JonathanFerron/MiyoCalc40/MiyoCalc40_firmware/cards.cpp

/*
  cards.c

*/

// includes
#include <stdint.h>
#include "cards.h"
#include "fonts.h"
#include "matrix.h"
#include "calc.h"
#include "config.h"

// defines


// structures

// global variables
const action ACT_0 = {KC_0, &enter_number, {0, MCFNULCHAR, MCFNULCHAR, MCFNULCHAR, MCFNULCHAR}};
const action ACT_1 = {KC_1, &enter_number, {1, MCFNULCHAR, MCFNULCHAR, MCFNULCHAR, MCFNULCHAR}};
const action ACT_2 = {KC_2, &enter_number, {2, MCFNULCHAR, MCFNULCHAR, MCFNULCHAR, MCFNULCHAR}};
const action ACT_3 = {KC_3, &enter_number, {3, MCFNULCHAR, MCFNULCHAR, MCFNULCHAR, MCFNULCHAR}};
const action ACT_4 = {KC_4, &enter_number, {4, MCFNULCHAR, MCFNULCHAR, MCFNULCHAR, MCFNULCHAR}};
const action ACT_5 = {KC_5, &enter_number, {5, MCFNULCHAR, MCFNULCHAR, MCFNULCHAR, MCFNULCHAR}};
const action ACT_6 = {KC_6, &enter_number, {6, MCFNULCHAR, MCFNULCHAR, MCFNULCHAR, MCFNULCHAR}};
const action ACT_7 = {KC_7, &enter_number, {7, MCFNULCHAR, MCFNULCHAR, MCFNULCHAR, MCFNULCHAR}};
const action ACT_8 = {KC_8, &enter_number, {8, MCFNULCHAR, MCFNULCHAR, MCFNULCHAR, MCFNULCHAR}};
const action ACT_9 = {KC_9, &enter_number, {9, MCFNULCHAR, MCFNULCHAR, MCFNULCHAR, MCFNULCHAR}};
const action ACT_A = {KC_A, &enter_number, {'A' - MCFLETOFFSET, MCFNULCHAR, MCFNULCHAR, MCFNULCHAR, MCFNULCHAR}};
const action ACT_B = {KC_B, &enter_number, {'B' - MCFLETOFFSET, MCFNULCHAR, MCFNULCHAR, MCFNULCHAR, MCFNULCHAR}};
const action ACT_C = {KC_C, &enter_number, {'C' - MCFLETOFFSET, MCFNULCHAR, MCFNULCHAR, MCFNULCHAR, MCFNULCHAR}};
const action ACT_D = {KC_D, &enter_number, {'D' - MCFLETOFFSET, MCFNULCHAR, MCFNULCHAR, MCFNULCHAR, MCFNULCHAR}};
const action ACT_E = {KC_E, &enter_number, {'E' - MCFLETOFFSET, MCFNULCHAR, MCFNULCHAR, MCFNULCHAR, MCFNULCHAR}};
const action ACT_F = {KC_F, &enter_number, {'F' - MCFLETOFFSET, MCFNULCHAR, MCFNULCHAR, MCFNULCHAR, MCFNULCHAR}};

const action ACT_POINT = {KC_POINT, &enter_decpoint, {MCFNULCHAR, MCFNULCHAR, MCFNULCHAR, MCFNULCHAR, MCFNULCHAR}};  // need to implement a decimal point character in the main font table
const action ACT_CHGSGN = {KC_CHGSGN, &enter_sign, {39, 36, MCFNULCHAR, MCFNULCHAR, MCFNULCHAR}};
const action ACT_EEX = {KC_EEX, &enter_exp, {'E' - MCFLETOFFSET, MCFNULCHAR, MCFNULCHAR, MCFNULCHAR, MCFNULCHAR}};
const action ACT_PI = {KC_PI, &apply_const, {47, MCFNULCHAR, MCFNULCHAR, MCFNULCHAR, MCFNULCHAR}};

const action ACT_ADD = {KC_ADD, &apply_func_2to1, {39, MCFNULCHAR, MCFNULCHAR, MCFNULCHAR, MCFNULCHAR}};
const action ACT_SUBS = {KC_SUBS, &apply_func_2to1, {36, MCFNULCHAR, MCFNULCHAR, MCFNULCHAR, MCFNULCHAR}};
const action ACT_MULT = {KC_MULT, &apply_func_2to1, {'X' - MCFLETOFFSET, MCFNULCHAR, MCFNULCHAR, MCFNULCHAR, MCFNULCHAR}};  // need to implement a multiplication character in the main font table
const action ACT_DIV = {KC_DIV, &apply_func_2to1, {45, MCFNULCHAR, MCFNULCHAR, MCFNULCHAR, MCFNULCHAR}};
const action ACT_POW = {KC_POW, &apply_func_2to1, {'P' - MCFLETOFFSET, 'O' - MCFLETOFFSET, 'W' - MCFLETOFFSET, MCFNULCHAR, MCFNULCHAR}};
const action ACT_ROOT = {KC_ROOT, &apply_func_2to1, {'R' - MCFLETOFFSET, 'O' - MCFLETOFFSET, 'O' - MCFLETOFFSET, 'T' - MCFLETOFFSET, MCFNULCHAR}};
const action ACT_MULTINV = {KC_MULTINV, &apply_func_1to1, {1, 45, 'X' - MCFLETOFFSET, MCFNULCHAR, MCFNULCHAR}};
const action ACT_ABS = {KC_ABS, &apply_func_1to1, {'A' - MCFLETOFFSET, 'B' - MCFLETOFFSET, 'S' - MCFLETOFFSET, MCFNULCHAR, MCFNULCHAR}};
const action ACT_SQRT = {KC_SQRT, &apply_func_1to1, {'S' - MCFLETOFFSET, 'Q' - MCFLETOFFSET, 'R' - MCFLETOFFSET, 'T' - MCFLETOFFSET, MCFNULCHAR}};
const action ACT_SQUARE = {KC_SQUARE, &apply_func_1to1, {'X' - MCFLETOFFSET, 42, 2, MCFNULCHAR, MCFNULCHAR}};
const action ACT_LN = {KC_LN, &apply_func_1to1, {'L' - MCFLETOFFSET, 'N' - MCFLETOFFSET, MCFNULCHAR, MCFNULCHAR, MCFNULCHAR}};
const action ACT_EXP = {KC_EXP, &apply_func_1to1, {'E' - MCFLETOFFSET, 'X' - MCFLETOFFSET, 'P' - MCFLETOFFSET, MCFNULCHAR, MCFNULCHAR}};
const action ACT_FACT = {KC_FACT, &apply_func_1to1, {'F' - MCFLETOFFSET, 'A' - MCFLETOFFSET, 'C' - MCFLETOFFSET, 'T' - MCFLETOFFSET, MCFNULCHAR}};
const action ACT_ROUND = {KC_ROUND, &apply_func_1to1, {'R' - MCFLETOFFSET, 'O' - MCFLETOFFSET, 'U' - MCFLETOFFSET, 'N' - MCFLETOFFSET, 'D' - MCFLETOFFSET}};
const action ACT_FRAC = {KC_FRAC, &apply_func_1to1, {'F' - MCFLETOFFSET, 'R' - MCFLETOFFSET, 'A' - MCFLETOFFSET, 'C' - MCFLETOFFSET, MCFNULCHAR}};
const action ACT_INTEG = {KC_INTEG, &apply_func_1to1, {'I' - MCFLETOFFSET, 'N' - MCFLETOFFSET, 'T' - MCFLETOFFSET, 'E' - MCFLETOFFSET, 'G' - MCFLETOFFSET}};

const action ACT_ENTER = {KC_ENTER, &enter_enter, {'E' - MCFLETOFFSET, 'N' - MCFLETOFFSET, 'T' - MCFLETOFFSET, 'E' - MCFLETOFFSET, 'R' - MCFLETOFFSET}};
const action ACT_DROPX = {KC_DROPX, &enter_drop, {'D' - MCFLETOFFSET, 'R' - MCFLETOFFSET, 'O' - MCFLETOFFSET, 'P' - MCFLETOFFSET, 'X' - MCFLETOFFSET}};
const action ACT_SWAP = {KC_SWAP, &enter_swap_xy, {'X' - MCFLETOFFSET, 37, 36, 38, 'Y' - MCFLETOFFSET}};
const action ACT_ROLLDN = {KC_ROLLDN, &enter_rotate, {'R' - MCFLETOFFSET, 'O' - MCFLETOFFSET, 'L' - MCFLETOFFSET, 'D' - MCFLETOFFSET, 'N' - MCFLETOFFSET}};
const action ACT_ROLLUP = {KC_ROLLUP, &enter_rotate, {'R' - MCFLETOFFSET, 'O' - MCFLETOFFSET, 'L' - MCFLETOFFSET, 'U' - MCFLETOFFSET, 'P' - MCFLETOFFSET}};
const action ACT_BKSCLRX = {KC_BKSCLRX, &enter_backspace_clrx, {'C' - MCFLETOFFSET, 'L' - MCFLETOFFSET, 'R' - MCFLETOFFSET, 'X' - MCFLETOFFSET, MCFNULCHAR}};
const action ACT_LASTX = {KC_LASTX, &enter_lastx, {'L' - MCFLETOFFSET, 'A' - MCFLETOFFSET, 'S' - MCFLETOFFSET, 'T' - MCFLETOFFSET, 'X' - MCFLETOFFSET}};
const action ACT_CLRSTCK = {KC_CLRSTCK, &enter_clear, {'C' - MCFLETOFFSET, 'L' - MCFLETOFFSET, 'S' - MCFLETOFFSET, 'T' - MCFLETOFFSET, 'K' - MCFLETOFFSET}};

const action ACT_STOREG = {KC_STOREG, &toggle_mem_mode, {'S' - MCFLETOFFSET, 'T' - MCFLETOFFSET, 'O' - MCFLETOFFSET, 'R' - MCFLETOFFSET, 'G' - MCFLETOFFSET}};
const action ACT_RCLREG = {KC_RCLREG, &toggle_mem_mode, {'R' - MCFLETOFFSET, 'C' - MCFLETOFFSET, 'L' - MCFLETOFFSET, 'R' - MCFLETOFFSET, 'G' - MCFLETOFFSET}};
const action ACT_CLRREG = {KC_CLRREG, &toggle_mem_mode, {'C' - MCFLETOFFSET, 'L' - MCFLETOFFSET, 'R' - MCFLETOFFSET, 'R' - MCFLETOFFSET, 'G' - MCFLETOFFSET}};

const action ACT_SIN = {KC_SIN, &apply_func_1to1, {'S' - MCFLETOFFSET, 'I' - MCFLETOFFSET, 'N' - MCFLETOFFSET, MCFNULCHAR, MCFNULCHAR}};
const action ACT_COS = {KC_COS, &apply_func_1to1, {'S' - MCFLETOFFSET, 'I' - MCFLETOFFSET, 'N' - MCFLETOFFSET, MCFNULCHAR, MCFNULCHAR}};
const action ACT_TAN = {KC_TAN, &apply_func_1to1, {'S' - MCFLETOFFSET, 'I' - MCFLETOFFSET, 'N' - MCFLETOFFSET, MCFNULCHAR, MCFNULCHAR}};
const action ACT_ASIN = {KC_ASIN, &apply_func_1to1, {'S' - MCFLETOFFSET, 'I' - MCFLETOFFSET, 'N' - MCFLETOFFSET, MCFNULCHAR, MCFNULCHAR}};
const action ACT_ACOS = {KC_ACOS, &apply_func_1to1, {'S' - MCFLETOFFSET, 'I' - MCFLETOFFSET, 'N' - MCFLETOFFSET, MCFNULCHAR, MCFNULCHAR}};
const action ACT_ATAN = {KC_ATAN, &apply_func_1to1, {'S' - MCFLETOFFSET, 'I' - MCFLETOFFSET, 'N' - MCFLETOFFSET, MCFNULCHAR, MCFNULCHAR}};

//const action ACT_BWAND = {KC_BWAND, &apply_func_2to1, {, , , ,}};
//const action ACT_BWOR = {KC_BWOR, &apply_func_2to1, {, , , ,}};
//const action ACT_BWXOR = {KC_BWXOR, &apply_func_2to1, {, , , ,}};
//const action ACT_BWNOT = {KC_BWNOT, &apply_func_1to1, {, , , ,}};

//const action ACT_MODEBIN = {KC_MODEBIN, &change_nbr_rep_mode, {, , , ,}};
//const action ACT_MODEOCT = {KC_MODEOCT, &change_nbr_rep_mode, {, , , ,}};
//const action ACT_MODEDEC = {KC_MODEDEC, &change_nbr_rep_mode, {, , , ,}};
//const action ACT_MODEHEX = {KC_MODEHEX, &change_nbr_rep_mode, {, , , ,}};

const action ACT_MODERAD = {KC_MODERAD, &set_trig_mode, {'R' - MCFLETOFFSET, 'A' - MCFLETOFFSET, 'D' - MCFLETOFFSET, MCFNULCHAR, MCFNULCHAR}};
const action ACT_MODEDEG = {KC_MODEDEG, &set_trig_mode, {'D' - MCFLETOFFSET, 'E' - MCFLETOFFSET, 'G' - MCFLETOFFSET, MCFNULCHAR, MCFNULCHAR}};

//const action ACT_DATE = {KC_DATE, &apply_func_2to1, {, , , ,}};
//const action ACT_DATEDIFF = {KC_DATEDIFF, &apply_func_2to1, {, , , ,}};

const action ACT_NOP = {KC_NOP, &do_nothing, {'N' - MCFLETOFFSET, 'O' - MCFLETOFFSET, 'P' - MCFLETOFFSET, MCFNULCHAR, MCFNULCHAR}};

const action ACT_SHFT_B = {KC_NOP, &enter_shift_base, {'B' - MCFLETOFFSET, MCFNULCHAR, MCFNULCHAR, MCFNULCHAR, MCFNULCHAR}};
const action ACT_SHFT_F = {KC_NOP, &enter_shift_f, {'F' - MCFLETOFFSET, MCFNULCHAR, MCFNULCHAR, MCFNULCHAR, MCFNULCHAR}};
const action ACT_SHFT_G = {KC_NOP, &enter_shift_g, {'G' - MCFLETOFFSET, MCFNULCHAR, MCFNULCHAR, MCFNULCHAR, MCFNULCHAR}};
const action ACT_SHFT_H = {KC_NOP, &enter_shift_h, {'H' - MCFLETOFFSET, MCFNULCHAR, MCFNULCHAR, MCFNULCHAR, MCFNULCHAR}};

const action ACT_PWR_DOWN = {KC_NOP, &power_down, {MCFNULCHAR, MCFNULCHAR, MCFNULCHAR, MCFNULCHAR, MCFNULCHAR}};

const action ACT_CALC_MOD = {KC_NOP, &enter_calc_mode, {MCFNULCHAR, MCFNULCHAR, MCFNULCHAR, MCFNULCHAR, MCFNULCHAR}};
const action ACT_CFG_MOD = {KC_NOP, &enter_config_mode, {MCFNULCHAR, MCFNULCHAR, MCFNULCHAR, MCFNULCHAR, MCFNULCHAR}};
const action ACT_PROG_MOD = {KC_NOP, &enter_prog_mode, {MCFNULCHAR, MCFNULCHAR, MCFNULCHAR, MCFNULCHAR, MCFNULCHAR}};

// config mode actions: none of these are programmable (all use KC_NOP as their keycode), since
// none of the 'config mode' functions are expected to be recordable in a program.
const action ACT_CFG_BATTVOLT = {KC_NOP, &config_show_battvolt, {'B' - MCFLETOFFSET, 'A' - MCFLETOFFSET, 'T' - MCFLETOFFSET, 'T' - MCFLETOFFSET, MCFNULCHAR}};
const action ACT_CFG_BACKLIGHT = {KC_NOP, &config_show_backlight, {'B' - MCFLETOFFSET, 'K' - MCFLETOFFSET, 'L' - MCFLETOFFSET, 'T' - MCFLETOFFSET, MCFNULCHAR}};
const action ACT_CFG_EXIT = {KC_NOP, &config_cancel_exit, {'E' - MCFLETOFFSET, 'X' - MCFLETOFFSET, 'I' - MCFLETOFFSET, 'T' - MCFLETOFFSET, MCFNULCHAR}};

// config-mode arrow keys: keycode carries the KCC_ direction (see cards.h) as config_adjust()'s
// argument rather than anything programmable -- config mode is never recorded into a program.
const action ACT_CFG_UP = {KCC_UP, &config_adjust, {MCFNULCHAR, MCFNULCHAR, MCFNULCHAR, MCFNULCHAR, MCFNULCHAR}};
const action ACT_CFG_DOWN = {KCC_DOWN, &config_adjust, {MCFNULCHAR, MCFNULCHAR, MCFNULCHAR, MCFNULCHAR, MCFNULCHAR}};
const action ACT_CFG_LEFT = {KCC_LEFT, &config_adjust, {MCFNULCHAR, MCFNULCHAR, MCFNULCHAR, MCFNULCHAR, MCFNULCHAR}};
const action ACT_CFG_RIGHT = {KCC_RIGHT, &config_adjust, {MCFNULCHAR, MCFNULCHAR, MCFNULCHAR, MCFNULCHAR, MCFNULCHAR}};

#define x____x &ACT_NOP

// define cards
// we should have 3 separate cards objects (calc_cards, prog_cards, config_card)


// calculator mode cards
const action *calc_cards[4][NUM_ROW_PINS][NUM_COLUMN_PINS] =
{ [baseLayer] =
  { {    &ACT_SWAP, &ACT_ENTER, &ACT_DROPX, &ACT_ROLLDN, &ACT_FACT, &ACT_ABS, &ACT_ROOT, &ACT_7, &ACT_8, &ACT_9}, // 10 columns in row 0 (top)
    { &ACT_BKSCLRX, &ACT_MULT, &ACT_DIV, &ACT_LN, &ACT_CLRSTCK, &ACT_CLRREG, &ACT_POW, &ACT_4, &ACT_5, &ACT_6}, // 10 columns in second row (row 1)
    {  &ACT_SQUARE, &ACT_ADD, &ACT_SUBS, &ACT_EXP, &ACT_STOREG, &ACT_RCLREG, &ACT_CHGSGN, &ACT_1, &ACT_2, &ACT_3},
    {   &ACT_LASTX, &ACT_MULTINV, &ACT_SQRT, &ACT_SIN, &ACT_PI, &ACT_COS, &ACT_TAN, &ACT_0, &ACT_POINT, &ACT_SHFT_F}
  },

  [fLayer] =
  { {       x____x,        x____x,        x____x, &ACT_ROLLUP,        x____x,        x____x,        x____x,        x____x,        x____x,        x____x},
    {       x____x,        x____x,        x____x,        x____x, &ACT_PROG_MOD,        x____x,        x____x,        x____x,        x____x,        x____x},
    {       x____x,        x____x,        x____x,        x____x,        x____x,        x____x,        x____x,        x____x,        x____x,        x____x},
    {       x____x,        x____x,        x____x, &ACT_ASIN, &ACT_PWR_DOWN, &ACT_ACOS, &ACT_ATAN, &ACT_MODERAD, &ACT_MODEDEG, &ACT_SHFT_G}
  },

  [gLayer] =
  { {       x____x,        x____x,        x____x,        x____x,        x____x,        x____x,        x____x,        x____x,        x____x,        x____x},
    {       x____x,        x____x,        x____x,        x____x,        x____x,        x____x,        x____x,        x____x,        x____x,        x____x},
    {       x____x,        x____x,        x____x,        x____x,        x____x,        x____x,        x____x,        x____x,        x____x,        x____x},
    {       x____x,        x____x,        x____x,        x____x,        x____x,        x____x,        x____x,        x____x,        x____x, &ACT_SHFT_H}
  },

  [hLayer] =
  { {       x____x,        x____x,        x____x,        x____x, &ACT_CFG_MOD,        x____x,        x____x,        x____x,        x____x,        x____x},
    {       x____x,        x____x,        x____x,        x____x,        x____x,        x____x,        x____x,        x____x,        x____x,        x____x},
    {       x____x,        x____x,        x____x,        x____x,        x____x,        x____x,        x____x,        x____x,        x____x,        x____x},
    {       x____x,        x____x,        x____x,        x____x,        x____x,        x____x,        x____x,        x____x,        x____x, &ACT_SHFT_B}
  },
};

// programming mode cards
const action *prog_cards[4][NUM_ROW_PINS][NUM_COLUMN_PINS] =
{ [baseLayer] =
  { {    x____x,        x____x,        x____x,        x____x,        x____x,        x____x,        x____x,        x____x,        x____x,        x____x},
    {       x____x,        x____x,        x____x,        x____x,        x____x,        x____x,        x____x,        x____x,        x____x,        x____x},
    {       x____x,        x____x,        x____x,        x____x,        x____x,        x____x,        x____x,        x____x,        x____x,        x____x},
    {       x____x,        x____x,        x____x,        x____x,        x____x,        x____x,        x____x,        x____x,        x____x,        x____x}
  },

  [fLayer] =
  { {    x____x,        x____x,        x____x,        x____x,        x____x,        x____x,        x____x,        x____x,        x____x,        x____x},
    {       x____x,        x____x,        x____x,        x____x,        x____x,        x____x,        x____x,        x____x,        x____x,        x____x},
    {       x____x,        x____x,        x____x,        x____x,        x____x,        x____x,        x____x,        x____x,        x____x,        x____x},
    {       x____x,        x____x,        x____x,        x____x,        x____x,        x____x,        x____x,        x____x,        x____x,        x____x}
  },

  [gLayer] =
  { {       x____x,        x____x,        x____x,        x____x,        x____x,        x____x,        x____x,        x____x,        x____x,        x____x},
    {       x____x,        x____x,        x____x,        x____x,        x____x,        x____x,        x____x,        x____x,        x____x,        x____x},
    {       x____x,        x____x,        x____x,        x____x,        x____x,        x____x,        x____x,        x____x,        x____x,        x____x},
    {       x____x,        x____x,        x____x,        x____x,        x____x,        x____x,        x____x,        x____x,        x____x,        x____x}
  },

  [hLayer] =
  { {     x____x,        x____x,        x____x,        x____x,        x____x,        x____x,        x____x,        x____x,        x____x,        x____x},
    {       x____x,        x____x,        x____x,        x____x,        x____x,        x____x,        x____x,        x____x,        x____x,        x____x},
    {       x____x,        x____x,        x____x,        x____x,        x____x,        x____x,        x____x,        x____x,        x____x,        x____x},
    {       x____x,        x____x,        x____x,        x____x,        x____x,        x____x,        x____x,        x____x,        x____x,        x____x}
  },
};

// config mode card
// layout per "ref card 40 x 6 plus notes - general scientific v2.svg" (bottom right, 'Config' section):
//
//   row  c0            c1              c2               c3            c4          c5           c6  c7  c8           c9
//   0    max stk size  import 1 pgm    import all pgm   -             down        up           -   7   8            9
//   1    stk mode      export 1 pgm    export all pgm   -             left        right        -   4   5            6
//   2    lcd 1/2 col   time out        -                -             -           -            -   1   2            3
//   3    debounce      lcd contrast    back light       -             batt volt   soft reset   -   0   cancel/exit  confirm
//
// 'batt volt', 'cancel/exit', and 'back light' (with its up/down/left/right adjustment) are
// wired up; the rest are placeholders (x____x) for upcoming passes.
const action *config_card[NUM_ROW_PINS][NUM_COLUMN_PINS] =
{ {       x____x,        x____x,        x____x,        x____x, &ACT_CFG_DOWN, &ACT_CFG_UP,        x____x,        x____x,        x____x,        x____x},
  {       x____x,        x____x,        x____x,        x____x, &ACT_CFG_LEFT, &ACT_CFG_RIGHT,     x____x,        x____x,        x____x,        x____x},
  {       x____x,        x____x,        x____x,        x____x,        x____x,        x____x,        x____x,        x____x,        x____x,        x____x},
  {       x____x,        x____x, &ACT_CFG_BACKLIGHT,    x____x, &ACT_CFG_BATTVOLT,     x____x,        x____x,        x____x, &ACT_CFG_EXIT,        x____x}
};


// function definitions

// from keypos_r and keypos_c (global variables), return an action structure, via a lookup of the keypos from the currently active card
/*
  keymap translation function: keytoaction(keypos)
  keypos: row and column number of key that was pressed, see matrix.c

  global variables used:
  mode: calc, prog, config

  do this:
  lookup from calccards, progcards, configcard matrices an 'action' structure:
    each 'card' could each be n x 4 x 10 matrices (n being 4 for calc mode and prog mode for unshifted, then f, g,
    and h, and n being 1 in the config mode)

  action structure: contains a keycode (for programming mode, if it's an action that's programmable, otherwise NOP=0xFF),
    a function pointer to the implementation of the actual action (function to always take
    one single argument, the keycode, though it may at time not be used, argument to be
    looked up and then 'provided' to the function called via the pointer), and a 'mnemonic' for the programming mode
    (uint8 matrix containing indexes of different characters from the 'font' table)

  return: the action structure
*/
action keytoaction()
{ // prog_cards exists but is currently just an all-NOP placeholder, unwired here
  // (programming mode is still design notes only, see programming.h), so prog_mode
  // falls through to calc_cards for now.
  if(current_calc_prog_config_mode == config_mode)
    return *config_card[keypos_r][keypos_c];
  // lookup action struct pointer in card and dereference it. will eventually add a first
  // dimension for the active 'card', variable name could be 'activecard'
  return *calc_cards[shift][keypos_r][keypos_c];
} // keytoaction()
