JonathanFerron/MiyoCalc40/MiyoCalc40_firmware/matrix.cpp

// Includes
#include <util/delay.h>

#include "matrix.h"
#include "gpio.h"

// Defines

// Global variables
//declare const for row pin and column pin arrays (contain pin numbers)
// rows from top (keypos_r=0 for row 1) to bottom (keypos_r=3 for row 4)
const gpio_pin_t row_pin_array[NUM_ROW_PINS] =
{ GPIO_PIN(PORTD, 0), GPIO_PIN(PORTD, 1), GPIO_PIN(PORTD, 2), GPIO_PIN(PORTD, 3)
};

// columns from left (keypos_c=0 for col A) to right (keypos_c=9 for col J)
const gpio_pin_t column_pin_array[NUM_COLUMN_PINS] =
{ GPIO_PIN(PORTC, 0), GPIO_PIN(PORTC, 1), GPIO_PIN(PORTC, 2), GPIO_PIN(PORTC, 3),
  GPIO_PIN(PORTD, 4), GPIO_PIN(PORTD, 5), GPIO_PIN(PORTD, 6), GPIO_PIN(PORTD, 7),
  GPIO_PIN(PORTF, 1), GPIO_PIN(PORTF, 0)
};

// PA0 and PA5 are unused pins; their digital input buffers are disabled
// below (PORTA.PINCTRLSET = 0b00100001, i.e. bit0 | bit5).

uint8_t keypos_r;
uint8_t keypos_c;


// helper matrix scanning functions code

void setupMatrix()
{ // set-up pull-up on column and row pins
  PORTA.PINCONFIG = PORT_PULLUPEN_bm;
  PORTC.PINCTRLSET = 0b00001111;
  PORTD.PINCTRLSET = 0b11111111;
  PORTF.PINCTRLSET = 0b00000011;

  // set-up column pins as input
  PORTC.DIRCLR = PIN0_bm | PIN1_bm | PIN2_bm | PIN3_bm;
  PORTD.DIRCLR = PIN4_bm | PIN5_bm | PIN6_bm | PIN7_bm;
  PORTF.DIRCLR = PIN0_bm | PIN1_bm;

  // set row pins as output low
  PORTD.DIRSET = PIN0_bm | PIN1_bm | PIN2_bm | PIN3_bm;
  PORTD.OUTCLR = PIN0_bm | PIN1_bm | PIN2_bm | PIN3_bm;

  // Disable the digital input buffer on the unused pins (porta.pin0ctrl = port_pullupen_bm | port_isc_input_disable_gc)
  PORTA.PINCONFIG = PORT_PULLUPEN_bm | PORT_ISC_INPUT_DISABLE_gc;
  PORTA.PINCTRLSET = 0b00100001;

  keypos_r = 0xff;  // initialize keypos to 'null', which we'll define as 0xff by convention, may want to define that as 'keyposnull' for readability
  keypos_c = 0xff;
}

/*
  Read each column to find which has been pulled low
  This will tell us which column was pressed

  Set column pins as output low
  set row pins as input

  Read each row to find which has been pulled low
  This will tell us which row was pressed

  reset columns pins to input and row pins as output low

  Combine row and column into a keypos struct and return the result (global var keypos)
*/
void scanKB()
{ // read each column to find if one has been pulled low
  for(uint8_t col = 0; col < NUM_COLUMN_PINS; col++)
  { if(GPIO_READ(column_pin_array[col]) == 0)
    { // we now know that 'c' is the column of the button pressed

      // set column pins as output low
      PORTC.DIRTGL = PIN0_bm | PIN1_bm | PIN2_bm | PIN3_bm;  // toggle direction to output
      PORTD.DIRTGL = PIN4_bm | PIN5_bm | PIN6_bm | PIN7_bm;
      PORTF.DIRTGL = PIN0_bm | PIN1_bm;

      PORTC.OUTCLR = PIN0_bm | PIN1_bm | PIN2_bm | PIN3_bm;  // low: can this be optimized out by running it just once in setupMatrix() ?
      PORTD.OUTCLR = PIN4_bm | PIN5_bm | PIN6_bm | PIN7_bm;
      PORTF.OUTCLR = PIN0_bm | PIN1_bm;

      // set row pins as input
      PORTD.DIRTGL = PIN0_bm | PIN1_bm | PIN2_bm | PIN3_bm;

      // Let the row pins settle before reading them: they were just switched
      // from driven-low output to input, and need time for the pull-up to
      // charge the line back up to a valid high level (through whatever
      // trace/diode capacitance sits on the row net) before a read is
      // trustworthy. The Arduino/DxCore build had enough incidental overhead
      // around this transition to mask the missing delay; this bare-metal
      // build's leaner codegen does not -- without it, every row read landed
      // on PD0 (row 0) regardless of which row was actually pressed, since
      // that's the first row checked and the one most likely to still be
      // mid-transition. 10us matches the design note this file already had
      // for exactly this transition (see the "Open RPN Calc" notes above).
      _delay_us(10);

      // Read each row to find which has been pulled low
      for(uint8_t row = 0; row < NUM_ROW_PINS; row++)
      { if(GPIO_READ(row_pin_array[row]) == 0)
        { // we now know that 'r' is the row of the button pressed
          // Combine row and column into a keypos struct and return the result (global var keypos)
          keypos_c = col;  // there is a cast from 8 to 4 bit here
          keypos_r = row;
          break;  // break out of the loop across each row
        }  // if a row pin was low

      } // loop across each row

      // reset columns pins to input and row pins as output low
      // column pins
      PORTC.DIRTGL = PIN0_bm | PIN1_bm | PIN2_bm | PIN3_bm;  // toggle direction to input
      PORTD.DIRTGL = PIN4_bm | PIN5_bm | PIN6_bm | PIN7_bm;
      PORTF.DIRTGL = PIN0_bm | PIN1_bm;

      // row pins
      PORTD.DIRTGL = PIN0_bm | PIN1_bm | PIN2_bm | PIN3_bm; // toggle direction to output
      PORTD.OUTCLR = PIN0_bm | PIN1_bm | PIN2_bm | PIN3_bm; // low: can this be optimized out as well by running it just once in setupMatrix() ?

      break;  // break out of the loop across each column
    } // if a column pin was low

  } // loop across each column

} // scanKB()
